deveworld/starboard/Firmware/qmk/starboard/keymaps/default/config.h

/* Copyright 2026 Starboard
 * SPDX-License-Identifier: GPL-2.0-or-later
 */

#pragma once

// OLED settings edited from the web configurator: 1 mode byte + 4 lines x 21 chars
#define EECONFIG_USER_DATA_SIZE 85
